MBerka/AccelRecorder/Firmware/wdt.h

/**
 * \file
 *
 * \brief AVR XMEGA WatchDog Timer driver.
 *
 * Copyright (C) 2011 Atmel Corporation. All rights reserved.
 *
 * \page License
 *
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
 * 3. The name of Atmel may not be used to endorse or promote products derived
 * from this software without specific prior written permission.
 *
 * 4. This software may only be redistributed and used in connection with an
 * Atmel AVR product.
 *
 * THIS SOFTWARE IS PROVIDED BY ATMEL "AS IS" AND ANY EXPRESS OR IMPLIED
 * WARRANTIES, INCLUDING, BUT NOT LIMITED TO, THE IMPLIED WARRANTIES OF
 * MERCHANTABILITY, FITNESS FOR A PARTICULAR PURPOSE AND NON-INFRINGEMENT ARE
 * EXPRESSLY AND SPECIFICALLY DISCLAIMED. IN NO EVENT SHALL ATMEL BE LIABLE FOR
 * ANY DIRECT, INDIRECT, INCIDENTAL, SPECIAL, EXEMPLARY, OR CONSEQUENTIAL
 * DAMAGES (INCLUDING, BUT NOT LIMITED TO, PROCUREMENT OF SUBSTITUTE GOODS OR
 * SERVICES; LOSS OF USE, DATA, OR PROFITS; OR BUSINESS INTERRUPTION) HOWEVER
 * CAUSED AND ON ANY THEORY OF LIABILITY, WHETHER IN CONTRACT, STRICT
 * LIABILITY, OR TORT (INCLUDING NEGLIGENCE OR OTHERWISE) ARISING IN ANY WAY
 * OUT OF THE USE OF THIS SOFTWARE, EVEN IF ADVISED OF THE POSSIBILITY OF SUCH
 * DAMAGE.
 */
#ifndef _WDT_H_
#define _WDT_H_

/// @cond 0
/**INDENT-OFF**/
#ifdef __cplusplus
extern "C" {
#endif
/**INDENT-ON**/
/// @endcond

//#include "compiler.h"
#include <avr/io.h>

/**
 * \defgroup wdt_group Watchdog Timer (WDT)
 *
 * This is a driver for configuring, enablig, disabling and use of the on-chip
 * WDT.
 *
 * \section dependencies Dependencies
 *
 * The WDT module depends on the following modules:
 *  - \ref ccp_group for writing in a CCP-protected 8-bit I/O register.
 *
 * @{
 */


//! Watchdog timeout period setting
enum wdt_timeout_period_t {
	//! Timeout period = 8 cycles or 8 ms @ 3.3V
	WDT_TIMEOUT_PERIOD_8CLK = (0x00),
	//! Timeout period = 16 cycles or 16 ms @ 3.3V
	WDT_TIMEOUT_PERIOD_16CLK = (0x01),
	//! Timeout period = 32 cycles or 32m s @ 3.3V
	WDT_TIMEOUT_PERIOD_32CLK = (0x02),
	//! Timeout period = 64 cycles or 64ms @ 3.3V
	WDT_TIMEOUT_PERIOD_64CLK = (0x03),
	//! Timeout period = 125 cycles or 125ms @ 3.3V
	WDT_TIMEOUT_PERIOD_125CLK = (0x04),
	//! 250 cycles or 250ms @ 3.3V)
	WDT_TIMEOUT_PERIOD_250CLK = (0x05),
	//! Timeout period = 500 cycles or 500ms @ 3.3V
	WDT_TIMEOUT_PERIOD_500CLK = (0x06),
	//! Timeout period =1K cycles or 1s @ 3.3V
	WDT_TIMEOUT_PERIOD_1KCLK = (0x07),
	//! Timeout period = 2K cycles or 2s @ 3.3V
	WDT_TIMEOUT_PERIOD_2KCLK = (0x08),
	//! Timeout period = 4K cycles or 4s @ 3.3V
	WDT_TIMEOUT_PERIOD_4KCLK = (0x09),
	//! Timeout period = 8K cycles or 8s @ 3.3V
	WDT_TIMEOUT_PERIOD_8KCLK = (0x0A),
};

//! Watchdog window period setting
enum wdt_window_period_t {
	//! Window period = 8 cycles or 8 ms @ 3.3V
	WDT_WINDOW_PERIOD_8CLK = (0x00),
	//! Window period = 16 cycles or 16 ms @ 3.3V
	WDT_WINDOW_PERIOD_16CLK = (0x01),
	//! Window period = 32 cycles or 32m s @ 3.3V
	WDT_WINDOW_PERIOD_32CLK = (0x02),
	//! Window period = 64 cycles or 64ms @ 3.3V
	WDT_WINDOW_PERIOD_64CLK = (0x03),
	//! Window period = 125 cycles or 125ms @ 3.3V
	WDT_WINDOW_PERIOD_125CLK = (0x04),
	//! 250 cycles or 250ms @ 3.3V)
	WDT_WINDOW_PERIOD_250CLK = (0x05),
	//! Window period = 500 cycles or 500ms @ 3.3V
	WDT_WINDOW_PERIOD_500CLK = (0x06),
	//! Window period =1K cycles or 1s @ 3.3V
	WDT_WINDOW_PERIOD_1KCLK = (0x07),
	//! Window period = 2K cycles or 2s @ 3.3V
	WDT_WINDOW_PERIOD_2KCLK = (0x08),
	//! Window period = 4K cycles or 4s @ 3.3V
	WDT_WINDOW_PERIOD_4KCLK = (0x09),
	//! Window period = 8K cycles or 8s @ 3.3V
	WDT_WINDOW_PERIOD_8KCLK = (0x0A),
};


/*! \brief This macro resets (clears/refreshes) the Watchdog Timer.
 */
// #if defined(__GNUC__)
// #define wdt_reset() __asm__ __volatile__("wdr");
// #elif defined(__ICCAVR__)
// #define wdt_reset() __watchdog_reset();
// #else
// #error Unsupported compiler.
// #endif


/*! \brief Wait until WD settings are synchronized to the WD clock domain.
 *
 */
static inline void wdt_wait_while_busy(void)
{
	while ((WDT.STATUS & WDT_SYNCBUSY_bm) == WDT_SYNCBUSY_bm) {
		// Wait until synchronization
	}
}


/*! \brief Check if the Watchdog Enable flag is set.
 *
 *  \retval  false  WDT disabled
 *           true   WDT enabled
 */
// static inline bool wdt_is_enabled(void)
// {
// 	return ((WDT.CTRL & WDT_ENABLE_bm) == WDT_ENABLE_bm);
// }


/*! \brief Check if the Watchdog Window mode flag is set.
 *
 *  \retval  false  WDT Window disabled
 *           true   WDT Window enabled
 */
// static inline bool wdt_window_mode_is_enabled(void)
// {
// 	return ((WDT.WINCTRL & WDT_WEN_bm) == WDT_WEN_bm);
// }

// 
// /*! \brief Gets the Watchdog timeout period.
//  *
//  *  This function reads the value of the WDT timeout period.
//  *
//  *  \retval  The WDT timeout period.
//  */
// static inline enum wdt_timeout_period_t wdt_get_timeout_period(void)
// {
// 	return ((enum wdt_timeout_period_t)
// 		((WDT.CTRL & WDT_PER_gm) >> WDT_PER_gp));
// }
// 
// 
// /*! \brief Gets the Watchdog window period.
//  *
//  *  This function reads the value of the WDT closed window coded period.
//  *
//  *  \retval  The WDT window period.
//  */
// static inline enum wdt_window_period_t wdt_get_window_period(void)
// {
// 	return ((enum wdt_window_period_t) 
// 		((WDT.WINCTRL & WDT_WPER_gm) >> WDT_WPER_gp));
// }
// 
// 
// /*! \brief Set Watchdog timeout period.
//  *
//  *  This function sets the coded field of the WDT timeout period.
//  *
//  *  The function writes the correct signature to the Configuration
//  *  Change Protection register before writing the CTRL register. Interrupts are
//  *  automatically ignored during the change enable period. The function will
//  *  wait for the WDT to be synchronized to the WDT clock domain before
//  *  proceeding
//  *
//  *  \param  to_period  WDT timeout coded period
//  */
// void wdt_set_timeout_period(enum wdt_timeout_period_t to_period);
// 
// 
// /*! \brief Set Watchdog window period.
//  *
//  *  This function sets the coded field of the WDT closed window period.
//  *  Note that this setting is available only if the WDT is enabled (hardware
//  *  behaviour relayed by software).
//  *
//  *  The function writes the correct signature to the Configuration
//  *  Change Protection register before writing the WINCTRL register. Interrupts
//  *  are automatically ignored during the change enable period. The function will
//  *  wait for the WDT to be synchronized to the WDT clock domain before
//  *  proceeding
//  *
//  *  \param  win_period  Window coded period
//  *
//  *  \retval  true   The WDT was enabled and the setting is done.
//  *           false  The WDT is disabled and the setting is discarded.
//  */
// bool wdt_set_window_period(enum wdt_window_period_t win_period);
// 

/*! \brief Disable Watchdog.
 *
 *  This function disables the WDT without changing period settings.
 *
 *  The function writes the correct signature to the Configuration
 *  Change Protection register before writing the CTRL register. Interrupts are
 *  automatically ignored during the change enable period. Disable functions
 *  operate asynchronously with immidiate effect.
 */
void wdt_disable(void);


/*! \brief Enable Watchdog.
 *
 *  This function enables the WDT without changing period settings.
 *
 *  The function writes the correct signature to the Configuration
 *  Change Protection register before writing the CTRL register. Interrupts are
 *  automatically ignored during the change enable period. The function will
 *  wait for the WDT to be synchronized to the WDT clock domain before
 *  proceeding
 */
void wdt_enable(void);


// /*! \brief Disable Watchdog window mode without changing period settings.
//  *
//  *  This function disables the WDT window mode without changing period settings.
//  *
//  *  The function writes the correct signature to the Configuration
//  *  Change Protection register before writing the WINCTRL register. Interrupts
//  *  are automatically ignored during the change enable period. Disable functions
//  *  operate asynchronously with immidiate effect.
//  *
//  *  \retval  true   The WDT was enabled and the window mode is disabled.
//  *           false  The WDT (& the window mode) is already disabled.
//  */
// bool wdt_disable_window_mode(void);
// 
// 
// /*! \brief Enable Watchdog window mode.
//  *
//  *  This function enables the WDT window mode without changing period settings.
//  *
//  *  The function writes the correct signature to the Configuration
//  *  Change Protection register before writing the WINCTRL register. Interrupts
//  *  are automatically ignored during the change enable period. The function will
//  *  wait for the WDT to be synchronized to the WDT clock domain before
//  *  proceeding
//  *
//  *  \retval  true   The WDT was enabled and the setting is done.
//  *           false  The WDT is disabled and the setting is discarded.
//  */
// bool wdt_enable_window_mode(void);
// 
// 
// /*! \brief Reset MCU via Watchdog.
//  *
//  *  This function generates an hardware microcontroller reset using the WDT.
//  *
//  *  The function loads enables the WDT in window mode. Executing a "wdr" asm
//  *  instruction when the windows is closed, provides a quick mcu reset.
//  *
//  */
// void wdt_reset_mcu(void);
// 
// 
// //! @}
// 
// /// @cond 0
// /**INDENT-OFF**/
// #ifdef __cplusplus
// }
// #endif
// /**INDENT-ON**/
// /// @endcond
#endif // _WDT_H_
